oleg-politechnik/walkgeek/include/nuttx/mm.h

/****************************************************************************
 * include/nuttx/mm.h
 *
 *   Copyright (C) 2007-2009, 2013 Gregory Nutt. All rights reserved.
 *   Author: Gregory Nutt <gnutt@nuttx.org>
 *
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
 * 1. Redistributions of source code must retain the above copyright
 *    notice, this list of conditions and the following disclaimer.
 * 2. Redistributions in binary form must reproduce the above copyright
 *    notice, this list of conditions and the following disclaimer in
 *    the documentation and/or other materials provided with the
 *    distribution.
 * 3. Neither the name NuttX nor the names of its contributors may be
 *    used to endorse or promote products derived from this software
 *    without specific prior written permission.
 *
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
 ****************************************************************************/

#ifndef __INCLUDE_NUTTX_MM_H
#define __INCLUDE_NUTTX_MM_H

/****************************************************************************
 * Included Files
 ****************************************************************************/

#include <nuttx/config.h>

#include <sys/types.h>

/****************************************************************************
 * Pre-Processor Definitions
 ****************************************************************************/
/* Configuration ************************************************************/
/* If the MCU has a small (16-bit) address capability, then we will use
 * a smaller chunk header that contains 16-bit size/offset information.
 * We will also use the smaller header on MCUs with wider addresses if
 * CONFIG_MM_SMALL is selected.  This configuration is common with MCUs
 * that have a large FLASH space, but only a tiny internal SRAM.
 */

#ifdef CONFIG_SMALL_MEMORY
  /* If the MCU has a small addressing capability, then for the smaller
   * chunk header.
   */

#  undef  CONFIG_MM_SMALL
#  define CONFIG_MM_SMALL 1
#endif

/* Chunk Header Definitions *************************************************/
/* These definitions define the characteristics of allocator
 *
 * MM_MIN_SHIFT is used to define MM_MIN_CHUNK.
 * MM_MIN_CHUNK - is the smallest physical chunk that can
 *   be allocated.  It must be at least a large as
 *   sizeof(struct mm_freenode_s).  Larger values may
 *   improve performance slightly, but will waste memory
 *   due to quantization losses.
 *
 * MM_MAX_SHIFT is used to define MM_MAX_CHUNK
 * MM_MAX_CHUNK is the largest, contiguous chunk of memory
 *   that can be allocated.  It can range from 16-bytes to
 *   4Gb.  Larger values of MM_MAX_SHIFT can cause larger
 *   data structure sizes and, perhaps, minor performance
 *   losses.
 */

#ifdef CONFIG_MM_SMALL
#  define MM_MIN_SHIFT    4  /* 16 bytes */
#  define MM_MAX_SHIFT   15  /* 32 Kb */
#else
#  define MM_MIN_SHIFT    4  /* 16 bytes */
#  define MM_MAX_SHIFT   22  /*  4 Mb */
#endif

/* All other definitions derive from these two */

#define MM_MIN_CHUNK     (1 << MM_MIN_SHIFT)
#define MM_MAX_CHUNK     (1 << MM_MAX_SHIFT)
#define MM_NNODES        (MM_MAX_SHIFT - MM_MIN_SHIFT + 1)

#define MM_GRAN_MASK     (MM_MIN_CHUNK-1)
#define MM_ALIGN_UP(a)   (((a) + MM_GRAN_MASK) & ~MM_GRAN_MASK)
#define MM_ALIGN_DOWN(a) ((a) & ~MM_GRAN_MASK)

/* An allocated chunk is distinguished from a free chunk by bit 31 (or 15)
 * of the 'preceding' chunk size.  If set, then this is an allocated chunk.
 */

#ifdef CONFIG_MM_SMALL
# define MM_ALLOC_BIT    0x8000
#else
# define MM_ALLOC_BIT    0x80000000
#endif
#define MM_IS_ALLOCATED(n) \
  ((int)((struct mm_allocnode_s*)(n)->preceding) < 0))

/****************************************************************************
 * Public Types
 ****************************************************************************/

/* Determines the size of the chunk size/offset type */

#ifdef CONFIG_MM_SMALL
   typedef uint16_t mmsize_t;
#  define MMSIZE_MAX 0xffff
#else
   typedef size_t mmsize_t;
#  define MMSIZE_MAX SIZE_MAX
#endif

/* This describes an allocated chunk.  An allocated chunk is
 * distinguished from a free chunk by bit 15/31 of the 'preceding' chunk
 * size.  If set, then this is an allocated chunk.
 */

struct mm_allocnode_s
{
  mmsize_t size;           /* Size of this chunk */
  mmsize_t preceding;      /* Size of the preceding chunk */
};

/* What is the size of the allocnode? */

#ifdef CONFIG_MM_SMALL
# define SIZEOF_MM_ALLOCNODE   4
#else
# define SIZEOF_MM_ALLOCNODE   8
#endif

#define CHECK_ALLOCNODE_SIZE \
  DEBUGASSERT(sizeof(struct mm_allocnode_s) == SIZEOF_MM_ALLOCNODE)

/* This describes a free chunk */

struct mm_freenode_s
{
  mmsize_t size;                   /* Size of this chunk */
  mmsize_t preceding;              /* Size of the preceding chunk */
  FAR struct mm_freenode_s *flink; /* Supports a doubly linked list */
  FAR struct mm_freenode_s *blink;
};

/* What is the size of the freenode? */

#ifdef CONFIG_MM_SMALL
#  ifdef CONFIG_SMALL_MEMORY
#     define SIZEOF_MM_FREENODE 8
#  else
#     define SIZEOF_MM_FREENODE 12
#  endif
#else
# define SIZEOF_MM_FREENODE     16
#endif

#define CHECK_FREENODE_SIZE \
  DEBUGASSERT(sizeof(struct mm_freenode_s) == SIZEOF_MM_FREENODE)

/* This describes one heap (possibly with multiple regions) */

struct mm_heap_s
{
  /* Mutually exclusive access to this data set is enforced with
   * the following un-named semaphore.
   */

  pid_t mm_holder;
  int   mm_counts_held;

  /* This is the size of the heap provided to mm */

  size_t  mm_heapsize;

  /* This is the first and last nodes of the heap */

  FAR struct mm_allocnode_s *mm_heapstart[CONFIG_MM_REGIONS];
  FAR struct mm_allocnode_s *mm_heapend[CONFIG_MM_REGIONS];

#if CONFIG_MM_REGIONS > 1
  int mm_nregions;
#endif

  /* All free nodes are maintained in a doubly linked list.  This
   * array provides some hooks into the list at various points to
   * speed searches for free nodes.
   */

  struct mm_freenode_s mm_nodelist[MM_NNODES];
};

/****************************************************************************
 * Public Data
 ****************************************************************************/

#undef EXTERN
#if defined(__cplusplus)
#define EXTERN extern "C"
extern "C"
{
#else
#define EXTERN extern
#endif

#if !defined(CONFIG_NUTTX_KERNEL) || !defined(__KERNEL__)
/* This is the user heap */

EXTERN struct mm_heap_s g_mmheap;

#endif

/****************************************************************************
 * Public Function Prototypes
 ****************************************************************************/

/* Functions contained in mm_initialize.c ***********************************/

void mm_initialize(FAR struct mm_heap_s *heap, FAR void *heap_start,
                   size_t heap_size);
void mm_addregion(FAR struct mm_heap_s *heap, FAR void *heapstart,
                  size_t heapsize);

/* Functions contained in umm_initialize.c **********************************/

#if !defined(CONFIG_NUTTX_KERNEL) || !defined(__KERNEL__)
void umm_initialize(FAR void *heap_start, size_t heap_size);
#endif

/* Functions contained in umm_addregion.c ***********************************/

#if !defined(CONFIG_NUTTX_KERNEL) || !defined(__KERNEL__)
void umm_addregion(FAR void *heapstart, size_t heapsize);
#endif

/* Functions contained in mm_sem.c ******************************************/

void mm_seminitialize(FAR struct mm_heap_s *heap);
void mm_takesemaphore(FAR struct mm_heap_s *heap);
int  mm_trysemaphore(FAR struct mm_heap_s *heap);
void mm_givesemaphore(FAR struct mm_heap_s *heap);

/* Functions contained in umm_semaphore.c ***********************************/

#if !defined(CONFIG_NUTTX_KERNEL) || !defined(__KERNEL__)
int  umm_trysemaphore(void);
void umm_givesemaphore(void);
#endif

/* Functions contained in mm_malloc.c ***************************************/

#ifdef CONFIG_MM_MULTIHEAP
FAR void *mm_malloc(FAR struct mm_heap_s *heap, size_t size);
#endif

/* Functions contained in mm_free.c *****************************************/

#ifdef CONFIG_MM_MULTIHEAP
void mm_free(FAR struct mm_heap_s *heap, FAR void *mem);
#endif

/* Functions contained in mm_realloc.c **************************************/

#ifdef CONFIG_MM_MULTIHEAP
FAR void *mm_realloc(FAR struct mm_heap_s *heap, FAR void *oldmem,
                     size_t size);
#endif

/* Functions contained in mm_calloc.c ***************************************/

#ifdef CONFIG_MM_MULTIHEAP
FAR void *mm_calloc(FAR struct mm_heap_s *heap, size_t n, size_t elem_size);
#endif

/* Functions contained in mm_zalloc.c ***************************************/

#ifdef CONFIG_MM_MULTIHEAP
FAR void *mm_zalloc(FAR struct mm_heap_s *heap, size_t size);
#endif

/* Functions contained in mm_memalign.c *************************************/

#ifdef CONFIG_MM_MULTIHEAP
FAR void *mm_memalign(FAR struct mm_heap_s *heap, size_t alignment,
                      size_t size);
#endif

/* Functions contained in mm_mallinfo.c *************************************/

#ifdef CONFIG_MM_MULTIHEAP
int  mm_mallinfo(FAR struct mm_heap_s *heap, FAR struct mallinfo *info);
#endif

/* Functions contained in mm_shrinkchunk.c **********************************/

void mm_shrinkchunk(FAR struct mm_heap_s *heap,
                    FAR struct mm_allocnode_s *node, size_t size);

/* Functions contained in mm_addfreechunk.c *********************************/

void mm_addfreechunk(FAR struct mm_heap_s *heap,
                     FAR struct mm_freenode_s *node);

/* Functions contained in mm_size2ndx.c.c ***********************************/

int mm_size2ndx(size_t size);

#undef EXTERN
#ifdef __cplusplus
}
#endif

#endif /* __INCLUDE_NUTTX_MM_H */
