oleg-politechnik/walkgeek/bsp/stm32f4xx/src/usbh_usr.c

/**
  ******************************************************************************
  * @file    Audio_playback_and_record/src/usbh_usr.c
  * @author  MCD Application Team
  * @version V1.0.0
  * @date    28-October-2011
  * @brief   This file includes the usb host user callbacks
  ******************************************************************************
  * @attention
  *
  * THE PRESENT FIRMWARE WHICH IS FOR GUIDANCE ONLY AIMS AT PROVIDING CUSTOMERS
  * WITH CODING INFORMATION REGARDING THEIR PRODUCTS IN ORDER FOR THEM TO SAVE
  * TIME. AS A RESULT, STMICROELECTRONICS SHALL NOT BE HELD LIABLE FOR ANY
  * DIRECT, INDIRECT OR CONSEQUENTIAL DAMAGES WITH RESPECT TO ANY CLAIMS ARISING
  * FROM THE CONTENT OF SUCH FIRMWARE AND/OR THE USE MADE BY CUSTOMERS OF THE
  * CODING INFORMATION CONTAINED HEREIN IN CONNECTION WITH THEIR PRODUCTS.
  *
  * <h2><center>&copy; COPYRIGHT 2011 STMicroelectronics</center></h2>
  ******************************************************************************
  */

/* Includes ------------------------------------------------------------------*/
#include "usbh_usr.h"
#include "stm32f4xx_it.h"
#include "system.h"
#include "player.h"

/** @addtogroup STM32F4-Discovery_Audio_Player_Recorder
  * @{
  */

/* External variables --------------------------------------------------------*/
/* Private typedef -----------------------------------------------------------*/
/* Private defines -----------------------------------------------------------*/
/* Private macros ------------------------------------------------------------*/
/* Private variables ---------------------------------------------------------*/
/*  Points to the DEVICE_PROP structure of current device */
/*  The purpose of this register is to speed up the execution */

USBH_Usr_cb_TypeDef USR_Callbacks =
{
  USBH_USR_Init,
  USBH_USR_DeInit,
  USBH_USR_DeviceAttached,
  USBH_USR_ResetDevice,
  USBH_USR_DeviceDisconnected,
  USBH_USR_OverCurrentDetected,
  USBH_USR_DeviceSpeedDetected,
  USBH_USR_Device_DescAvailable,
  USBH_USR_DeviceAddressAssigned,
  USBH_USR_Configuration_DescAvailable,
  USBH_USR_Manufacturer_String,
  USBH_USR_Product_String,
  USBH_USR_SerialNum_String,
  USBH_USR_EnumerationDone,
  USBH_USR_UserInput,
  USBH_USR_MSC_Application,
  USBH_USR_DeviceNotSupported,
  USBH_USR_UnrecoveredError
};

extern USB_OTG_CORE_HANDLE          USB_OTG_Core;

/* Private function prototypes -----------------------------------------------*/
/* Private functions ---------------------------------------------------------*/


/**
  * @brief  USBH_USR_Init
  * @param  None
  * @retval None
  */
void USBH_USR_Init(void)
{
  STM_EVAL_PBInit(BUTTON_USER, BUTTON_MODE_GPIO);
}

/**
  * @brief  USBH_USR_DeviceAttached
  * @param  None
  * @retval None
  */
void USBH_USR_DeviceAttached(void)
{

  /* Red LED off when device attached */
  STM_EVAL_LEDOff(LED5);
  /* Green LED on */
  STM_EVAL_LEDOn(LED4);
  /* TIM Interrupts enable */
  TIM_ITConfig(TIM4, TIM_IT_CC1, ENABLE);
}

/**
  * @brief  USBH_USR_UnrecoveredError
  * @param  None
  * @retval None
  */
void USBH_USR_UnrecoveredError (void)
{
}

/**
  * @brief  USBH_DisconnectEvent
  *         Device disconnect event
  * @param  None
  * @retval Staus
  */
void USBH_USR_DeviceDisconnected (void)
{
  /* Red Led on if the USB Key is removed */
  STM_EVAL_LEDOn(LED5);
  /* Disable the Timer */
  TIM_ITConfig(TIM4, TIM_IT_CC1 , DISABLE);

  BSP_PowerDisable();
}

/**
  * @brief  USBH_USR_ResetUSBDevice
  * @param  None
  * @retval None
  */
void USBH_USR_ResetDevice(void)
{
  /* callback for USB-Reset */
}


/**
  * @brief  USBH_USR_DeviceSpeedDetected
  *         Displays the message on LCD for device speed
  * @param  Device speed:
  * @retval None
  */
void USBH_USR_DeviceSpeedDetected(uint8_t DeviceSpeed)
{
}

/**
  * @brief  USBH_USR_Device_DescAvailable
  * @param  device descriptor
  * @retval None
  */
void USBH_USR_Device_DescAvailable(void *DeviceDesc)
{
  /* callback for device descriptor */
}

/**
  * @brief  USBH_USR_DeviceAddressAssigned
  *         USB device is successfully assigned the Address
  * @param  None
  * @retval None
  */
void USBH_USR_DeviceAddressAssigned(void)
{
  /* callback for device successfully assigned the Address */
}

/**
  * @brief  USBH_USR_Conf_Desc
  * @param  Configuration descriptor
  * @retval None
  */
void USBH_USR_Configuration_DescAvailable(USBH_CfgDesc_TypeDef * cfgDesc,
    USBH_InterfaceDesc_TypeDef *itfDesc,
    USBH_EpDesc_TypeDef *epDesc)
{
  /* callback for configuration descriptor */
}

/**
  * @brief  USBH_USR_Manufacturer_String
  * @param  Manufacturer String
  * @retval None
  */
void USBH_USR_Manufacturer_String(void *ManufacturerString)
{
  /* callback for  Manufacturer String */
}

/**
  * @brief  USBH_USR_Product_String
  * @param  Product String
  * @retval None
  */
void USBH_USR_Product_String(void *ProductString)
{
  /* callback for Product String */
}

/**
  * @brief  USBH_USR_SerialNum_String
  * @param  SerialNum_String
  * @retval None
  */
void USBH_USR_SerialNum_String(void *SerialNumString)
{
  /* callback for SerialNum_String */
}

/**
  * @brief  EnumerationDone
  *         User response request is displayed to ask application jump to class
  * @param  None
  * @retval None
  */
void USBH_USR_EnumerationDone(void)
{
  /* 0.5 seconds delay */
  USB_OTG_BSP_mDelay(500);
}

/**
  * @brief  USBH_USR_DeviceNotSupported
  *         Device is not supported
  * @param  None
  * @retval None
  */
void USBH_USR_DeviceNotSupported(void)
{
}


/**
  * @brief  USBH_USR_UserInput
  *         User Action for application state entry
  * @param  None
  * @retval USBH_USR_Status : User response for key button
  */
USBH_USR_Status USBH_USR_UserInput(void)
{
  /* callback for Key botton: set by software in this case */
  return USBH_USR_RESP_OK;
}

/**
  * @brief  USBH_USR_OverCurrentDetected
  *         Over Current Detected on VBUS
  * @param  None
  * @retval None
  */
void USBH_USR_OverCurrentDetected (void)
{
}

/**
  * @brief  USBH_USR_MSC_Application
  * @param  None
  * @retval Staus
  */
int USBH_USR_MSC_Application(void)
{
  static u32 last_ms;

//  System_SetState(SS_PLAYER);
//fixme
//  System_MainThread();

  return(0);
}

/**
  * @brief  USBH_USR_DeInit
  *         Deint User state and associated variables
  * @param  None
  * @retval None
  */
void USBH_USR_DeInit(void)
{
}

/**
  * @}
  */



/******************* (C) COPYRIGHT 2011 STMicroelectronics *****END OF FILE****/
