oleg-politechnik/walkgeek/bsp/stm32f4xx/inc/usbh_usr.h

/**
  ******************************************************************************
  * @file    Audio_playback_and_record/inc/usbh_usr.h
  * @author  MCD Application Team
  * @version V1.0.0
  * @date    28-October-2011
  * @brief   Header file for usbh_usr.c
  ******************************************************************************
  * @attention
  *
  * THE PRESENT FIRMWARE WHICH IS FOR GUIDANCE ONLY AIMS AT PROVIDING CUSTOMERS
  * WITH CODING INFORMATION REGARDING THEIR PRODUCTS IN ORDER FOR THEM TO SAVE
  * TIME. AS A RESULT, STMICROELECTRONICS SHALL NOT BE HELD LIABLE FOR ANY
  * DIRECT, INDIRECT OR CONSEQUENTIAL DAMAGES WITH RESPECT TO ANY CLAIMS ARISING
  * FROM THE CONTENT OF SUCH FIRMWARE AND/OR THE USE MADE BY CUSTOMERS OF THE
  * CODING INFORMATION CONTAINED HEREIN IN CONNECTION WITH THEIR PRODUCTS.
  *
  * <h2><center>&copy; COPYRIGHT 2011 STMicroelectronics</center></h2>
  ******************************************************************************
  */ 

/* Define to prevent recursive inclusion -------------------------------------*/
#ifndef __USH_USR_H__
#define __USH_USR_H__

#ifdef __cplusplus
 extern "C" {
#endif

/* Includes ------------------------------------------------------------------*/
#include "ff.h"
#include "stm32f4_discovery.h"
#include "usbh_core.h"
#include <stdio.h>
#include "usbh_msc_core.h"

/* Exported types ------------------------------------------------------------*/
/* Exported constants --------------------------------------------------------*/
/* Exported macros -----------------------------------------------------------*/
/* Exported variables --------------------------------------------------------*/
extern  USBH_Usr_cb_TypeDef USR_Callbacks;

/* Exported functions ------------------------------------------------------- */
void USB_Host_Init(void);

void USBH_USR_Init(void);
void USBH_USR_DeviceAttached(void);
void USBH_USR_ResetDevice(void);
void USBH_USR_DeviceDisconnected (void);
void USBH_USR_OverCurrentDetected (void);
void USBH_USR_DeviceSpeedDetected(uint8_t DeviceSpeed); 
void USBH_USR_Device_DescAvailable(void *);
void USBH_USR_DeviceAddressAssigned(void);
void USBH_USR_Configuration_DescAvailable(USBH_CfgDesc_TypeDef * cfgDesc,
                                          USBH_InterfaceDesc_TypeDef *itfDesc,
                                          USBH_EpDesc_TypeDef *epDesc);
void USBH_USR_Manufacturer_String(void *);
void USBH_USR_Product_String(void *);
void USBH_USR_SerialNum_String(void *);
void USBH_USR_EnumerationDone(void);
USBH_USR_Status USBH_USR_UserInput(void);
int USBH_USR_MSC_Application(void);
void USBH_USR_DeInit(void);
void USBH_USR_DeviceNotSupported(void);
void USBH_USR_UnrecoveredError(void);
#ifdef __cplusplus
}
#endif

#endif /*__USH_USR_H__*/

/******************* (C) COPYRIGHT 2011 STMicroelectronics *****END OF FILE****/
